rharpalani/InventoryIQ/notebooks/krish/img/quirc_object.png

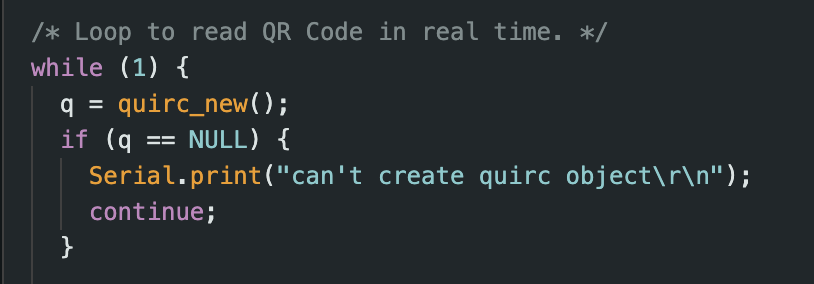
notebooks/krish/img/quirc_object.png
