rharpalani/InventoryIQ/notebooks/rohan/img/nov8.jpeg

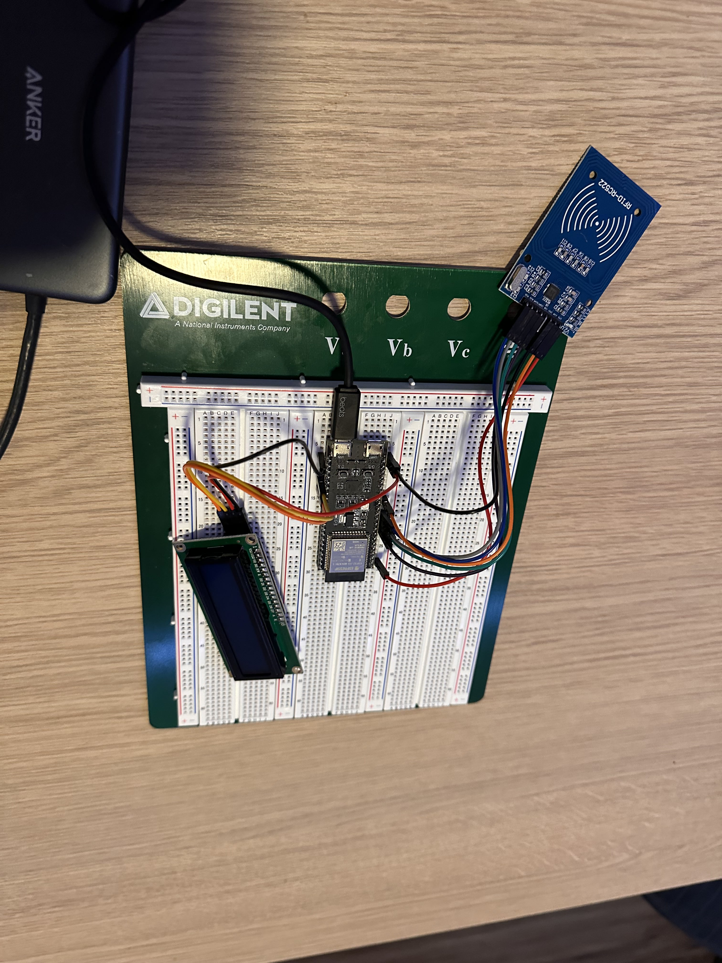
notebooks/rohan/img/nov8.jpeg
